Grix/helios_dac/media/20160925_094130.jpg

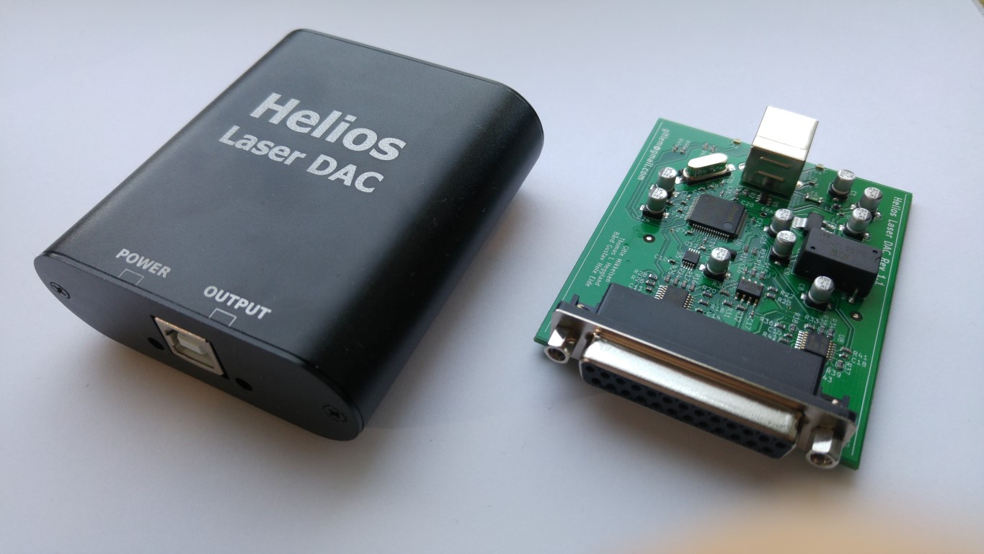
media/20160925_094130.jpg
