Grix/helios_dac/media/20160925_094215.jpg

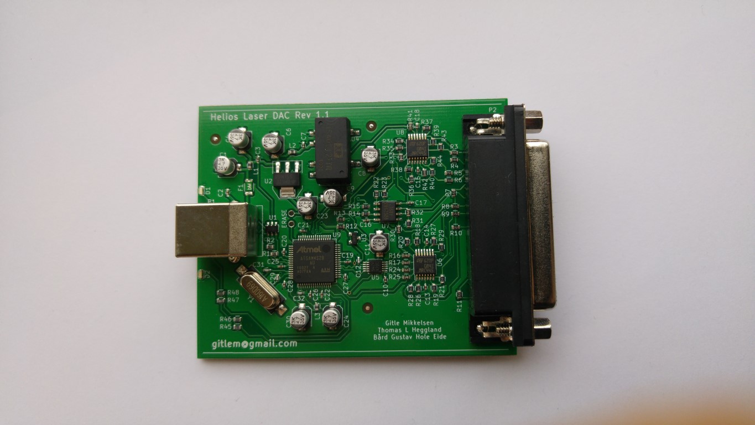
media/20160925_094215.jpg
