Grix/helios_dac/media/20160927_180950.jpg

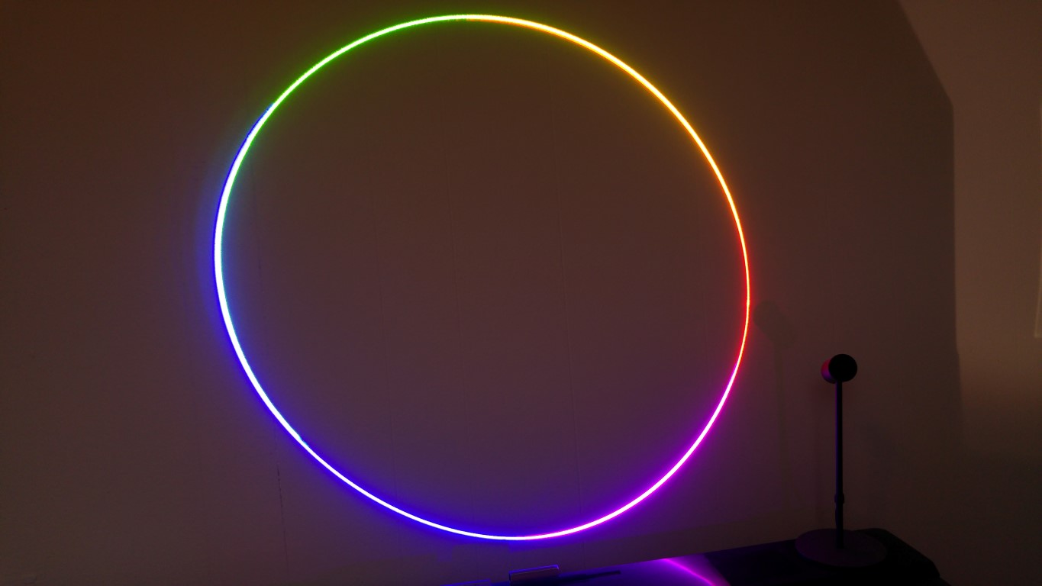
media/20160927_180950.jpg
