Grix/helios_dac/media/20160927_181319.jpg

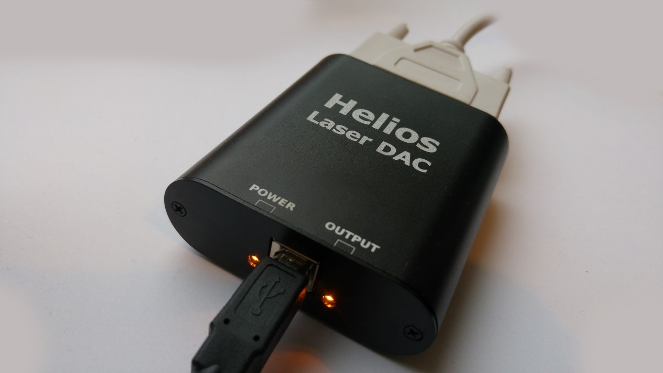
media/20160927_181319.jpg
