Grix/helios_dac/utility/UsbDiag/UsbDiag/HeliosDac.h

/*
Driver API for Helios Laser DAC class, HEADER
By Gitle Mikkelsen
gitlem@gmail.com

Dependencies:
Libusb 1.0 (GNU Lesser General Public License, see libusb.h)

Standard: C++14
git repo: https://github.com/Grix/helios_dac.git

BASIC USAGE:
1.	Call OpenDevices() to open devices, returns number of available devices.
2.	To send a new frame, first call GetStatus(). If the function returns ready (1), 
	then you can call WriteFrame(). The status should be polled until it returns ready. 
	It can and sometimes will fail to return ready on the first try.
3.  To stop output, use Stop(). To restart output you must send a new frame as described above.
4.	When the DAC is no longer needed, destroy the instance (destructors will free everything and close the connection)
*/

#pragma once

#include "libusb.h"
#include <cstring>
#include <cstdint>
#include <thread>
#include <mutex>
#include <vector>
#include <memory>
#include <chrono>
#include <future>

#define HELIOS_SDK_VERSION	5

#define HELIOS_MAX_POINTS	0x1000
#define HELIOS_MAX_RATE		0xFFFF
#define HELIOS_MIN_RATE		7

#define HELIOS_SUCCESS		1		
#define HELIOS_ERROR		-1		//functions return this if something went wrong
	
#define HELIOS_FLAGS_DEFAULT			0
#define HELIOS_FLAGS_START_IMMEDIATELY	(1 << 1)
#define HELIOS_FLAGS_SINGLE_MODE		(1 << 2)

//usb properties
#define HELIOS_VID	0x1209
#define HELIOS_PID	0xE500
#define EP_BULK_OUT	0x02
#define EP_BULK_IN	0x81
#define EP_INT_OUT	0x06
#define EP_INT_IN	0x83

#ifdef _DEBUG
#define LIBUSB_LOG_LEVEL LIBUSB_LOG_LEVEL_WARNING
#else
#define LIBUSB_LOG_LEVEL LIBUSB_LOG_LEVEL_NONE
#endif

//point data structure
typedef struct
{
	std::uint16_t x; //12 bit (from 0 to 0xFFF)
	std::uint16_t y; //12 bit (from 0 to 0xFFF)
	std::uint8_t r;	//8 bit	(from 0 to 0xFF)
	std::uint8_t g;	//8 bit (from 0 to 0xFF)
	std::uint8_t b;	//8 bit (from 0 to 0xFF)
	std::uint8_t i;	//8 bit (from 0 to 0xFF)
} HeliosPoint;

class HeliosDac
{
public:

	HeliosDac();
	~HeliosDac();

	//unless otherwise specified, functions return HELIOS_SUCCESS if OK, and HELIOS_ERROR if something went wrong.

	//initializes drivers, opens connection to all devices.
	//Returns number of available devices.
	//NB: To re-scan for newly connected DACs after this function has once been called before, you must first call CloseDevices()
	int OpenDevices();

	//closes and frees all devices
	int CloseDevices();

	//writes and outputs a frame to the speficied dac
	//devNum: dac number (0 to n where n+1 is the return value from OpenDevices() )
	//pps: rate of output in points per second
	//flags: (default is 0)
	//	Bit 0 (LSB) = if 1, start output immediately, instead of waiting for current frame (if there is one) to finish playing
	//	Bit 1 = if 1, play frame only once, instead of repeating until another frame is written
	//	Bit 2-7 = reserved
	//points: pointer to point data. See point structure declaration earlier in this document
	//NB! This function is asynchronous, so the points buffer must not be freed immediately after calling this function. It is safe to free
	//the points buffer once the status (GetStatus()) has returned to 1.
	//numOfPoints: number of points in the frame
	int WriteFrame(unsigned int devNum, unsigned int pps, std::uint8_t flags, HeliosPoint* points, unsigned int numOfPoints);

	//Gets status of DAC, 1 means DAC is ready to receive frame, 0 means it is not
	int GetStatus(unsigned int devNum);

	//Returns firmware version of DAC
	int GetFirmwareVersion(unsigned int devNum);

	//Gets name of DAC (populates name with max 32 characters)
	int GetName(unsigned int devNum, char* name);

	//Sets name of DAC (name must be max 31 characters incl. null terminator)
	int SetName(unsigned int devNum, char* name);

	//Stops output of DAC until new frame is written (NB: blocks for 100ms)
	int Stop(unsigned int devNum);

	//Sets shutter level of DAC
	int SetShutter(unsigned int devNum, bool level);

	//Erase the firmware of the DAC, allowing it to be updated by accessing the SAM-BA bootloader
	int EraseFirmware(unsigned int devNum);

private:

	class HeliosDacDevice
	{
	public:

		HeliosDacDevice(libusb_device_handle*);
		~HeliosDacDevice();
		int SendFrame(std::uint8_t* buffer, unsigned int bufferSize);
		int GetStatus();
		int GetFirmwareVersion();
		char* GetName();
		int SetName(char* name);
		int SetShutter(bool level);
		int Stop();
		int EraseFirmware();

	private:

		void DoFrame(std::uint8_t* buffer, unsigned int bufferSize);
		int SendControl(std::uint8_t* buffer, unsigned int bufferSize);

		struct libusb_transfer* interruptTransfer = NULL;
		struct libusb_device_handle* usbHandle;
		std::mutex frameLock;
		int firmwareVersion = 0;
		char name[32];
		bool closed = true;
	};

	std::vector<std::unique_ptr<HeliosDacDevice>> deviceList;
	std::mutex threadLock;
	bool inited = false;
};
